chizuchizu/bf-cpu/imgs/BF_DecArch_v1.png

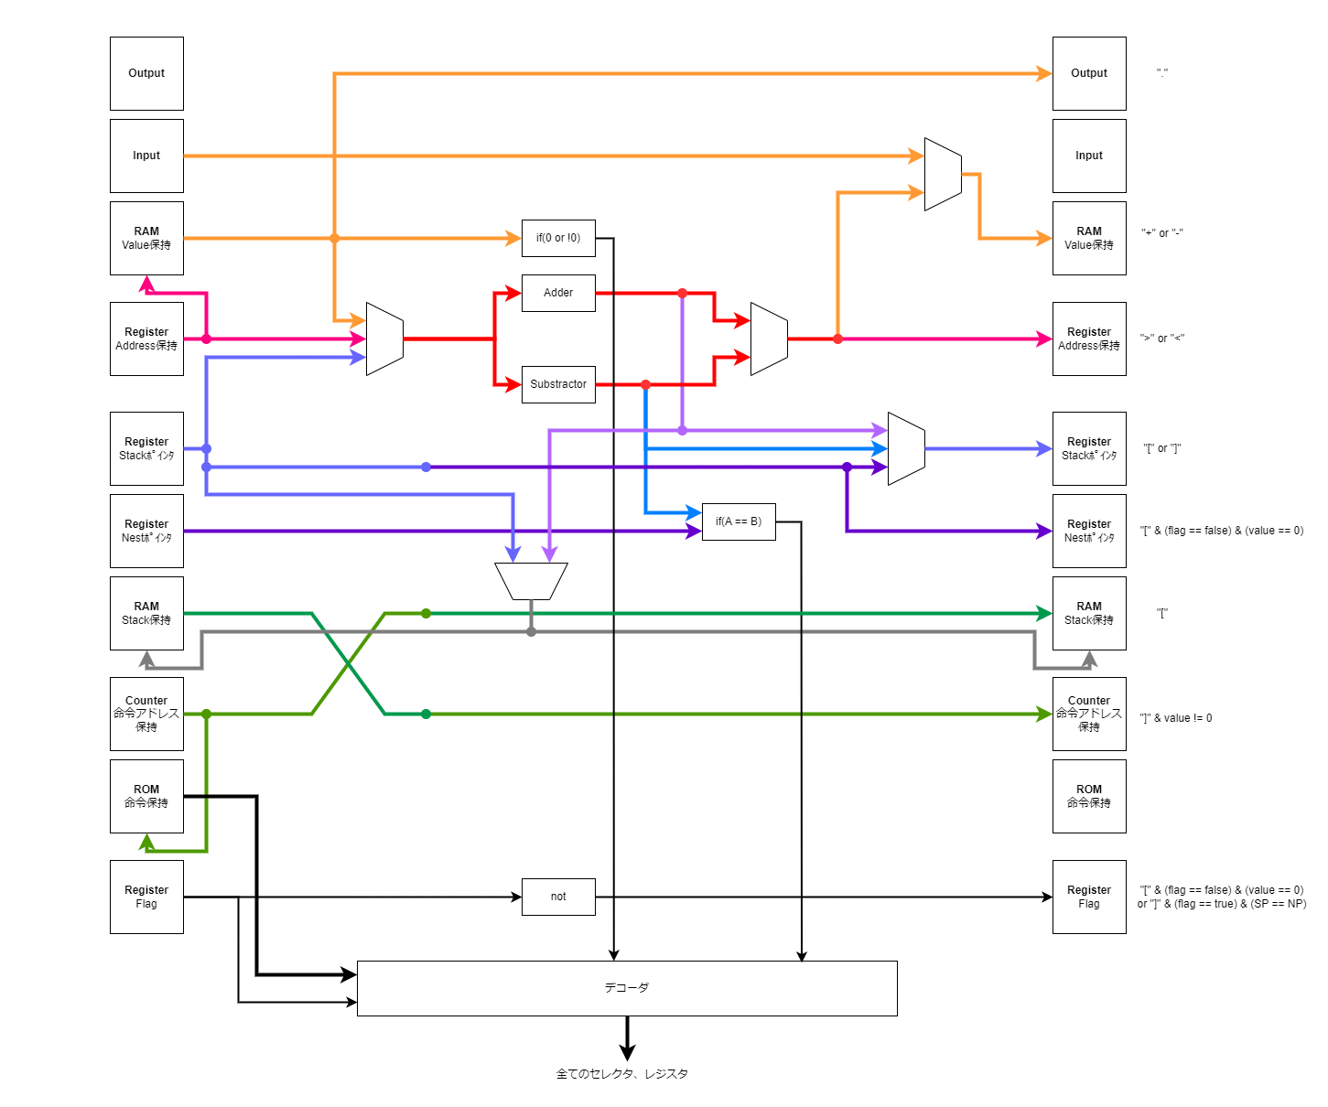
imgs/BF_DecArch_v1.png
