chizuchizu/bf-cpu/src/logicIC/logic_74HC32_tb.sv

module logic_74HC32_tb();

reg [3:0] in1;
reg [3:0] in2;
wire [3:0] out;

logic_74HC32 logic_74HC32_instance(
    .in1,
    .in2, 
    .out
);

initial begin
    $dumpfile("logic_74HC32.vcd");
    $dumpvars(1, logic_74HC32_tb);

    in1 = 4'b0011;
    in2 = 4'b0101;
    test_out(4'b0111);

    #5 in1 = 4'b1001;
       in2 = 4'b1010;
    #5 test_out(4'b1011);

    #5 in1 = 4'b1100;
       in2 = 4'b0101;
    #5 test_out(4'b1101);

    #5 in1 = 4'b0110;
       in2 = 4'b1010;
    #5 test_out(4'b1110);

    #5 $finish;
end

task test_out(
    input [3:0] ans
);
begin
    if (out != ans) $error("output must be %b but output is %b", ans, out);
end
endtask

endmodule
